NewieVentures/Obelisk/src/app/colours.h

#ifndef OBELISK_COLOURS_H
#define OBELISK_COLOURS_H

#include "colour.h"

#define COLOUR_BLACK Colour(0, 0, 0)
#define COLOUR_WHITE Colour(255, 255, 255)
#define COLOUR_RED Colour(255, 0, 0)
#define COLOUR_GREEN Colour(0, 255, 0)
#define COLOUR_BLUE Colour(0, 0, 255)
#define COLOUR_ORANGE Colour(0xFF, 0x7F, 0x00)
#define COLOUR_LIGHT_GREY Colour(150, 150, 150)
#define COLOUR_DARK_GREY Colour(50, 50, 50)
#define COLOUR_GOLDENROD_1 Colour(0xFF, 0xC1, 0x25)
#define COLOUR_DODGER_BLUE Colour(0x1E, 0x90, 0xFF)
#define COLOUR_DARK_GREEN Colour(0x00, 0x64, 0x00)
#define COLOUR_TURQUOISE Colour(0x40, 0xE0, 0xD0)

#endif
